cctweaker/epdash/webserver/imagini/compas.png

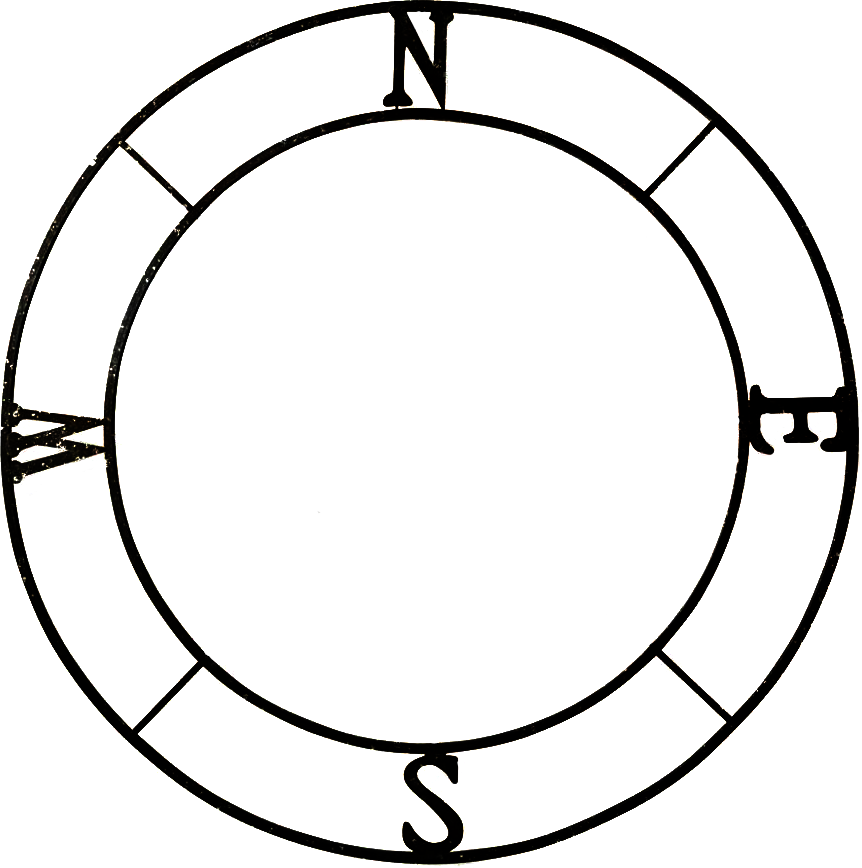
webserver/imagini/compas.png
