cctweaker/epdash/webserver/meteo/02d.png

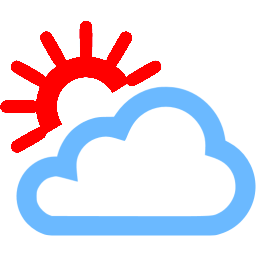
webserver/meteo/02d.png
