cctweaker/epdash/webserver/meteo/02n.png

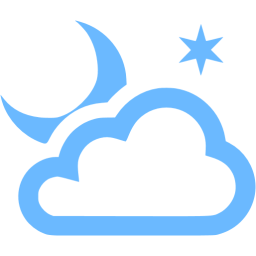
webserver/meteo/02n.png
