cctweaker/epdash/webserver/meteo/10d.png

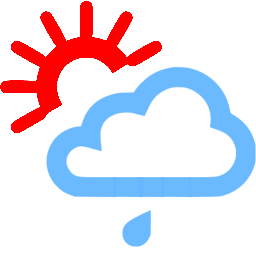
webserver/meteo/10d.png
