cctweaker/epdash/webserver/meteo/10n.png

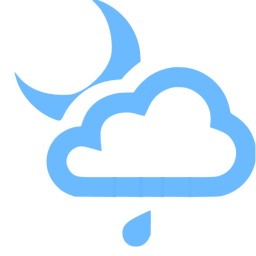
webserver/meteo/10n.png
