cctweaker/epdash/webserver/meteo/11d.png

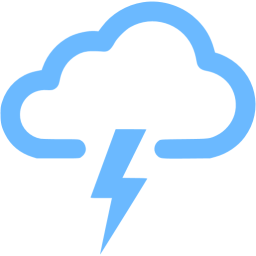
webserver/meteo/11d.png
