cctweaker/epdash/webserver/meteo/50d.png

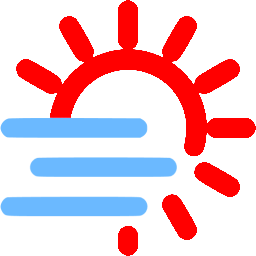
webserver/meteo/50d.png
