cctweaker/epdash/webserver/meteo/50n.png

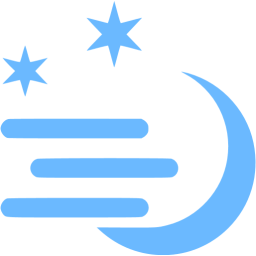
webserver/meteo/50n.png
