cctweaker/epdash/build_images/1.jpg

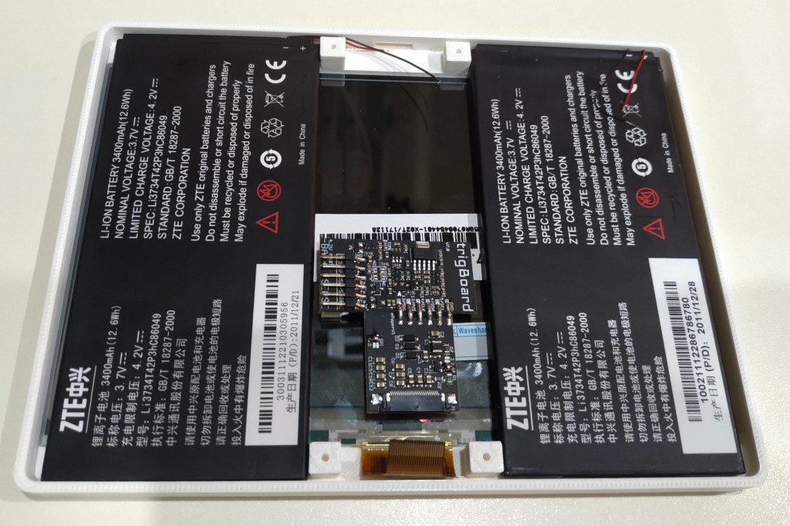
build_images/1.jpg
