cctweaker/epdash/build_images/2.jpg

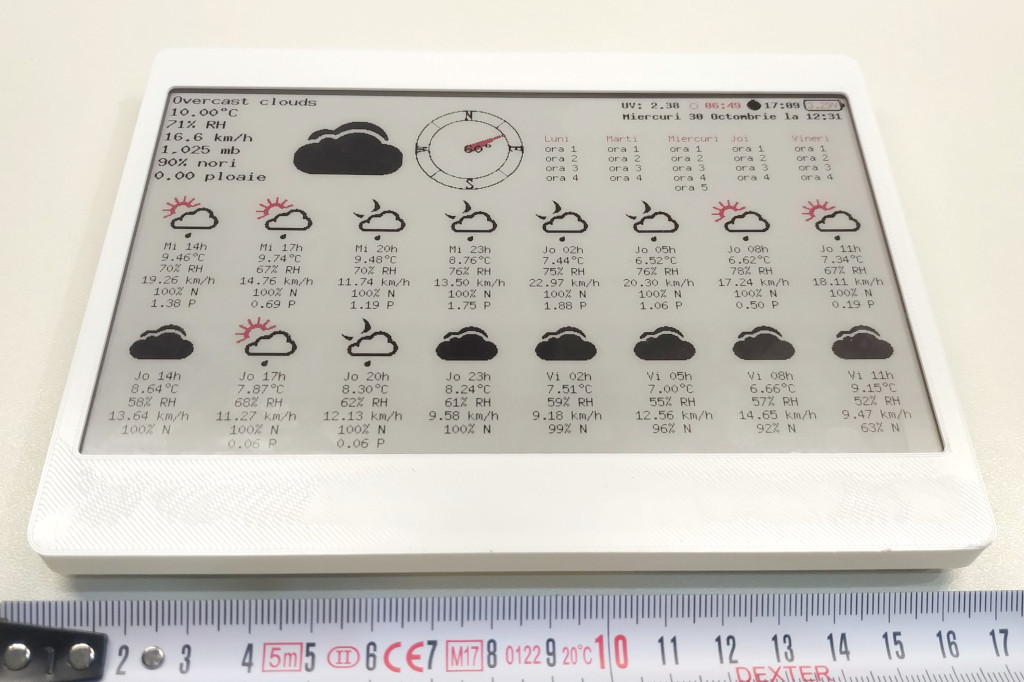
build_images/2.jpg
