cctweaker/epdash/build_images/3.jpg

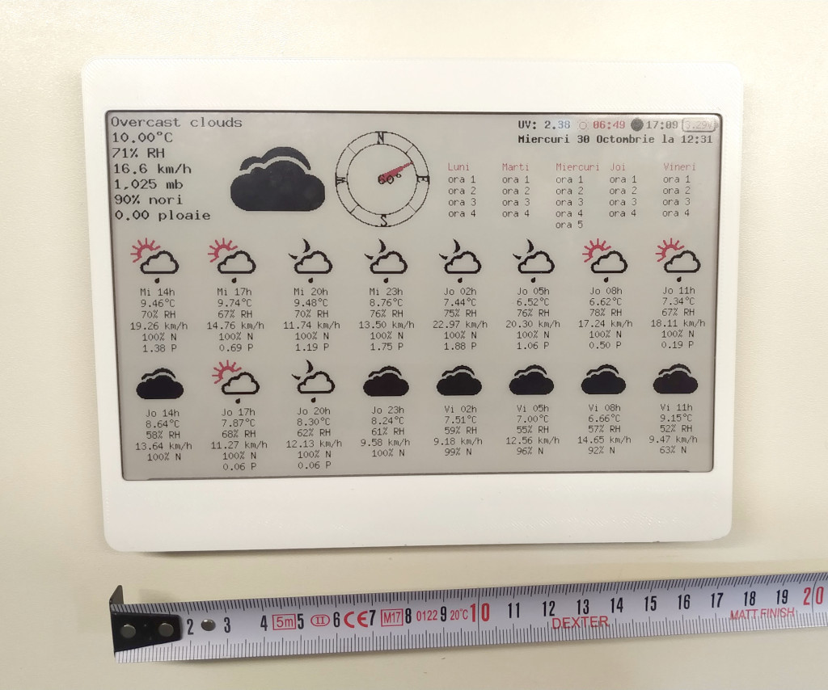
build_images/3.jpg
