cctweaker/epdash/build_images/4.jpg

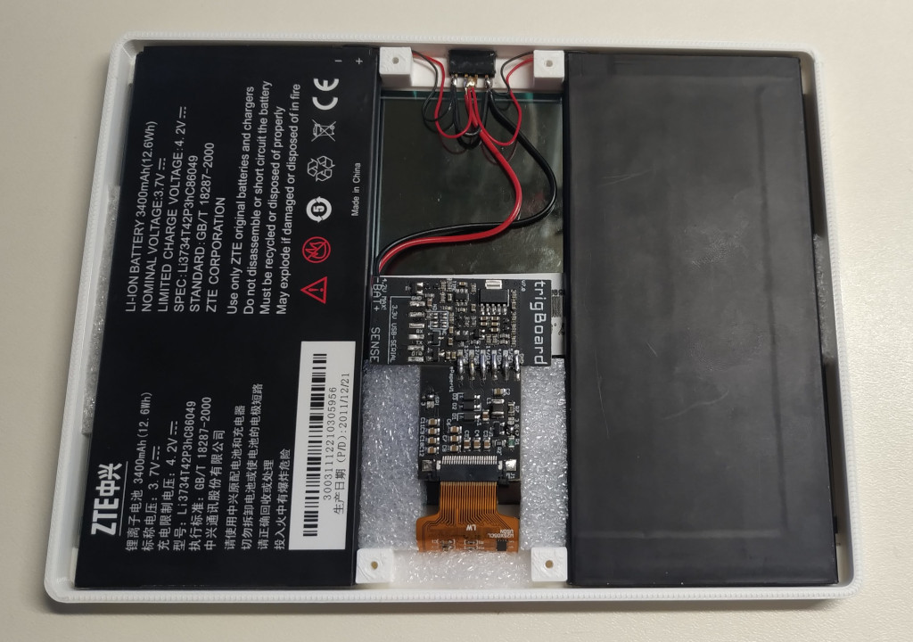
build_images/4.jpg
